tomekjaworski/SiloVibrationMeter/software/firmware/prev_prototype-1/spi_sw.h

#if !defined(_SPI_SW_H_)
#define _SPI_SW_H_

//void OpenSPI(void);
//void WriteSPI16(WORD value);
//void WriteSPI8(BYTE value);

void AMP_WriteSPI16(WORD value);
void AMP_ResetSPI(void);


#endif // _SPI_SW_H_
